togden/apiaster/images/also_in_mx_thanks_witch.jpg

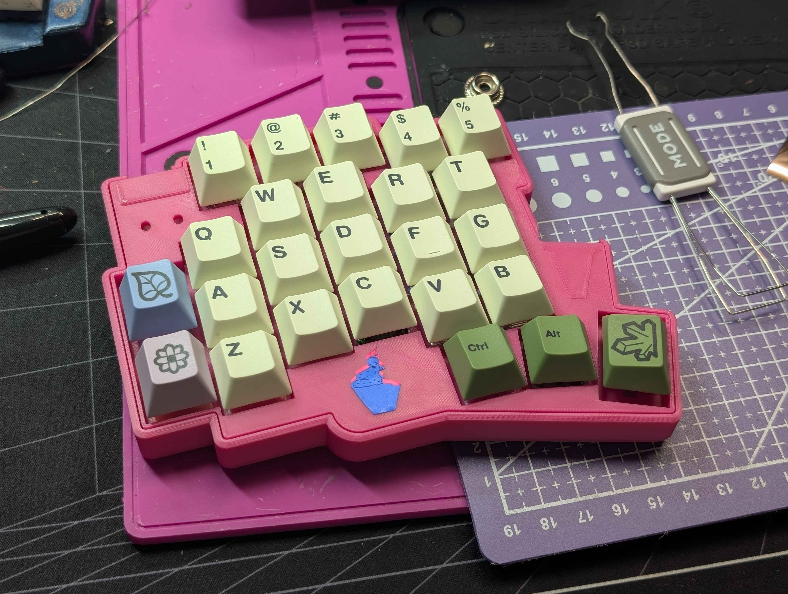
images/also_in_mx_thanks_witch.jpg
