togden/apiaster/images/ambient_choc.png

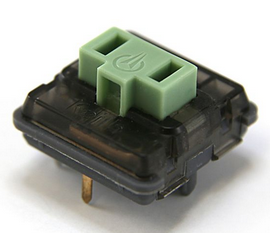
images/ambient_choc.png
