togden/apiaster/images/baby_kangaroo_mx.png

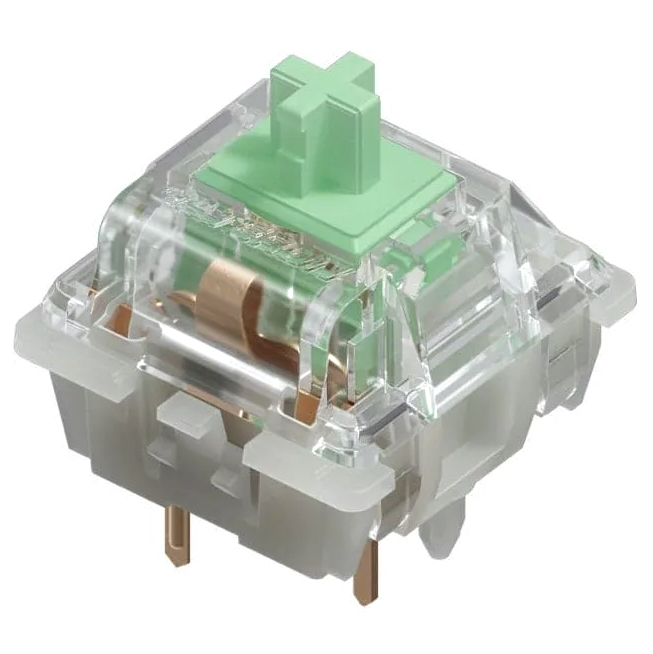
images/baby_kangaroo_mx.png
