togden/apiaster/images/coin_cell.png

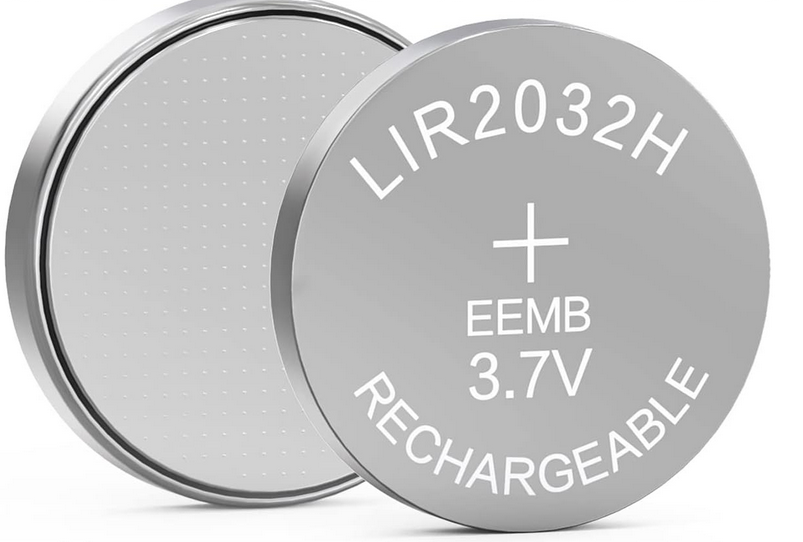
images/coin_cell.png
