togden/apiaster/images/front_angle.jpg

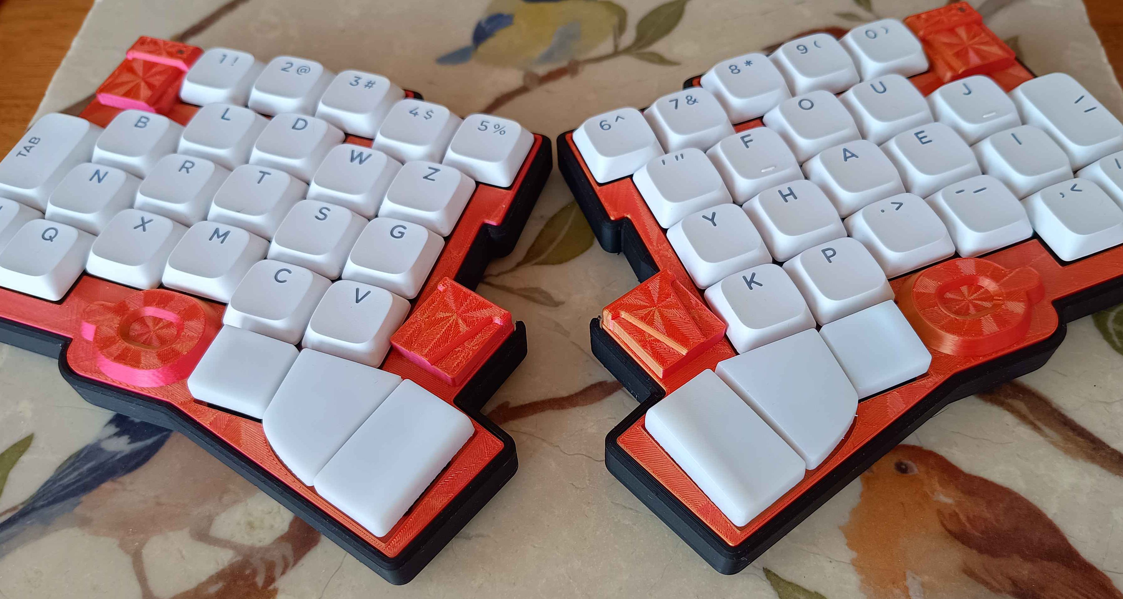
images/front_angle.jpg
