togden/apiaster/images/lipo-battery.png

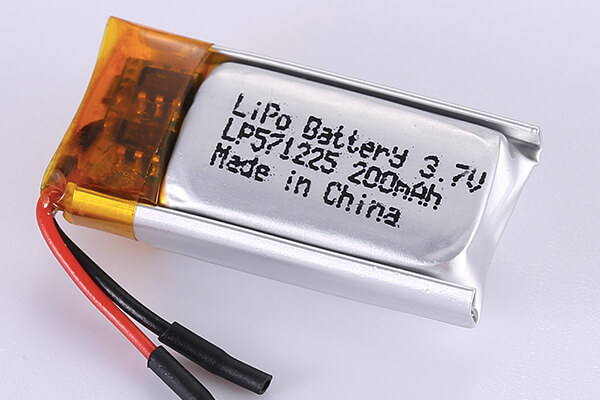
images/lipo-battery.png
