togden/apiaster/images/pom_chocv2.png

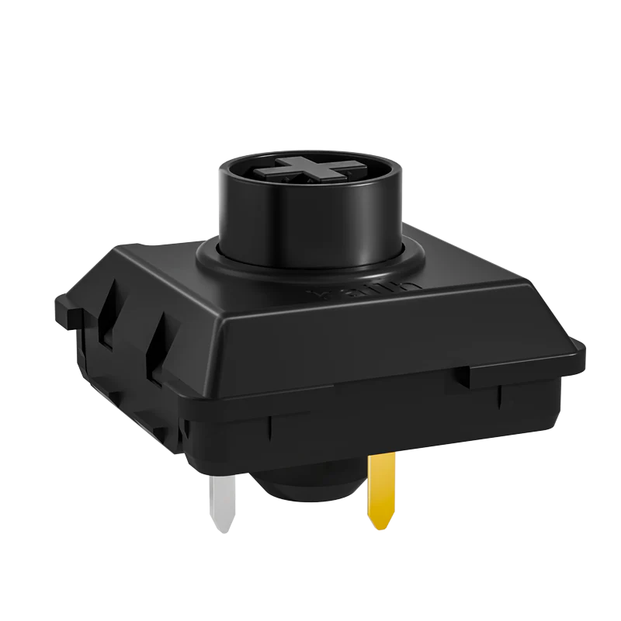
images/pom_chocv2.png
