togden/apiaster/images/rp2040-zero.png

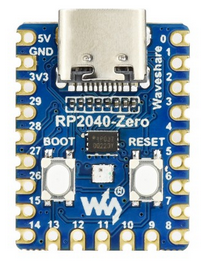
images/rp2040-zero.png
