togden/apiaster/images/show_rpi_caps.jpg

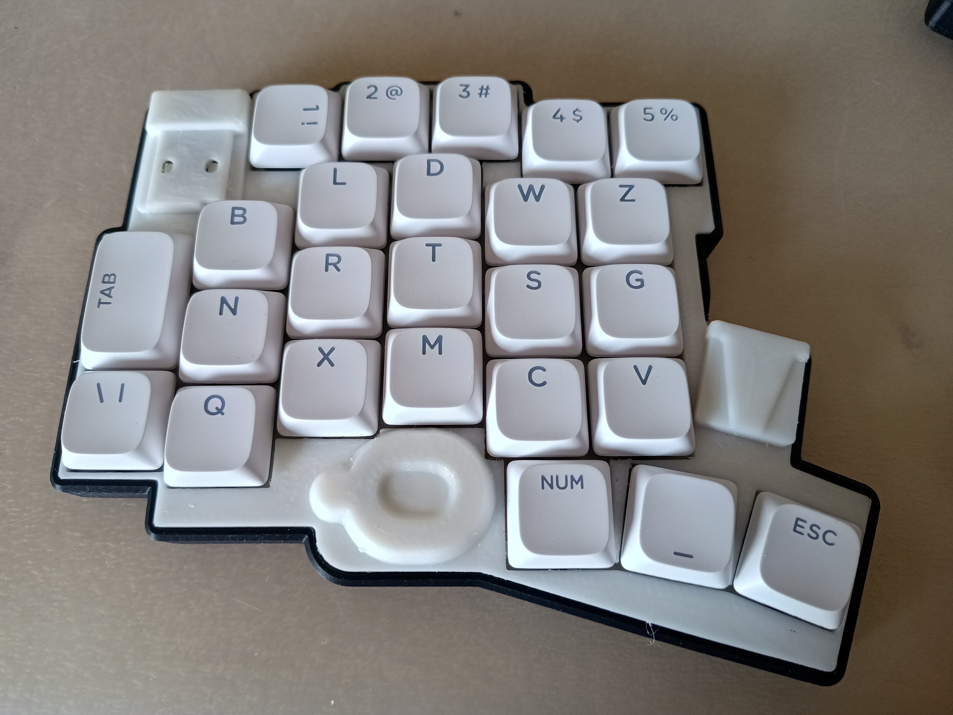
images/show_rpi_caps.jpg
