togden/apiaster/images/show_rpi_no_caps.jpg

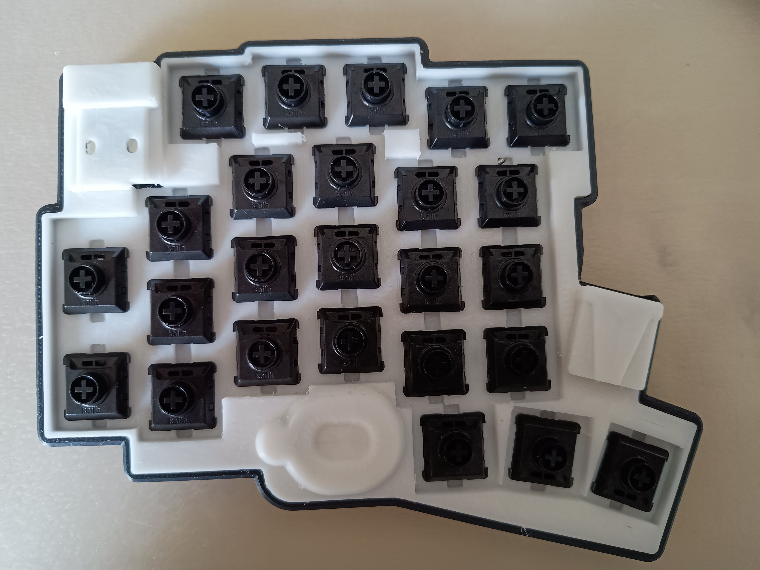
images/show_rpi_no_caps.jpg
