togden/apiaster/images/thickness.jpg

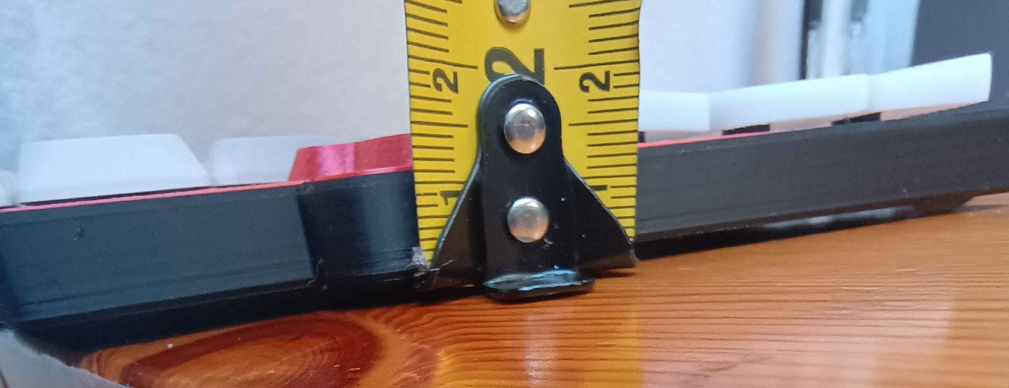
images/thickness.jpg
