togden/apiaster/images/upper.jpg

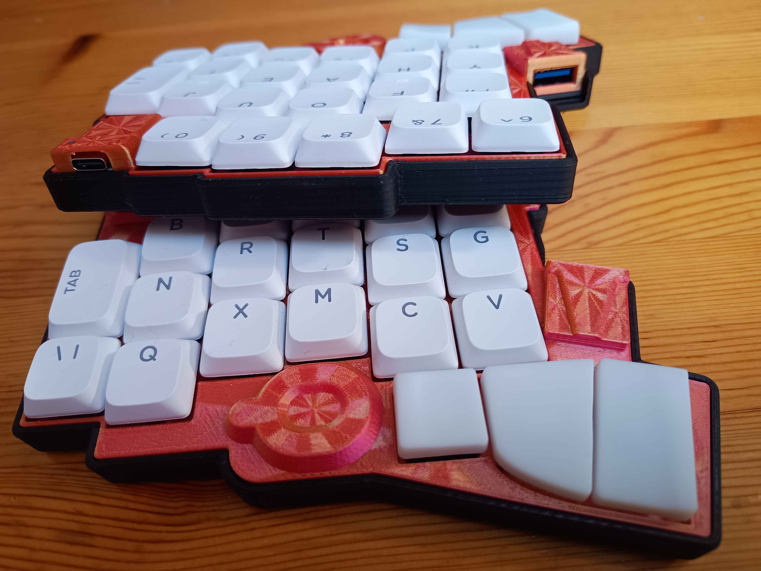
images/upper.jpg
