togden/apiaster/images/xiao.png

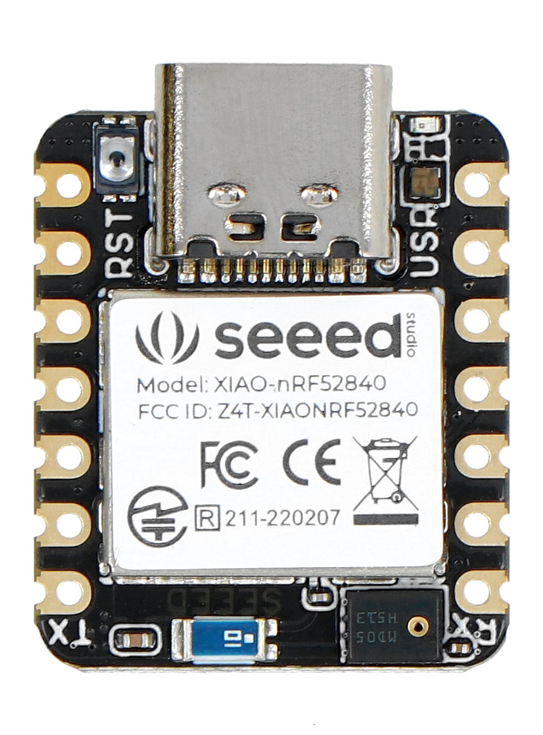
images/xiao.png
