togden/apiaster/images/build-guide/1_base_pcb_3_diodes.jpg

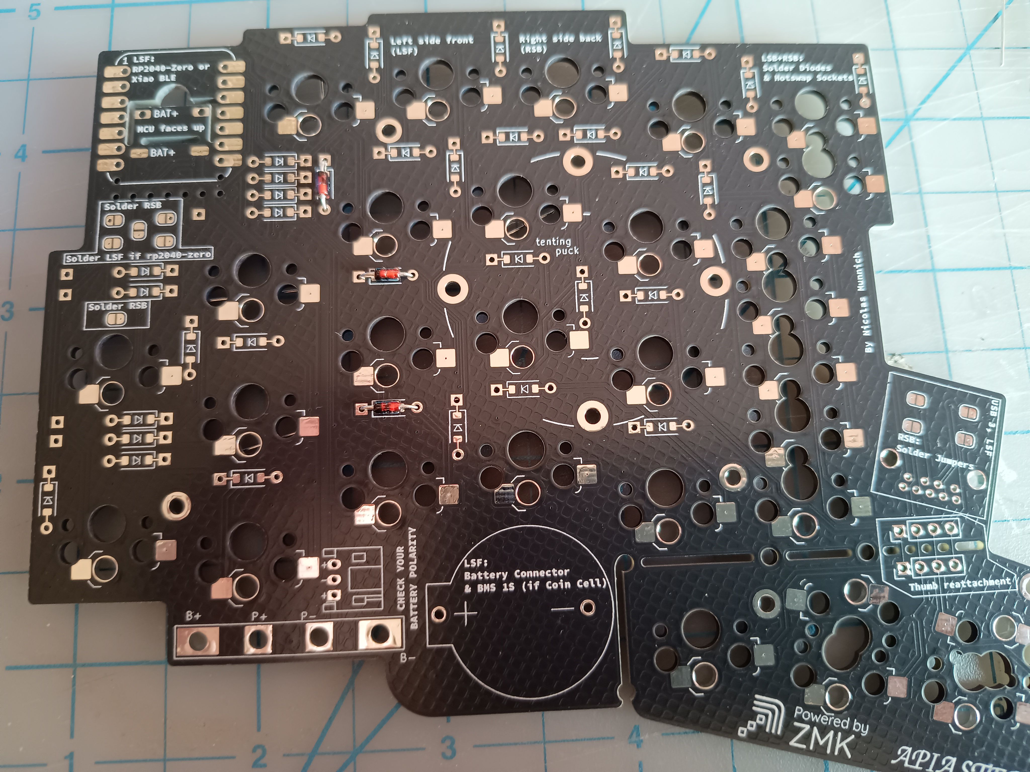
images/build-guide/1_base_pcb_3_diodes.jpg
