togden/apiaster/images/build-guide/5_check_orientation.jpg

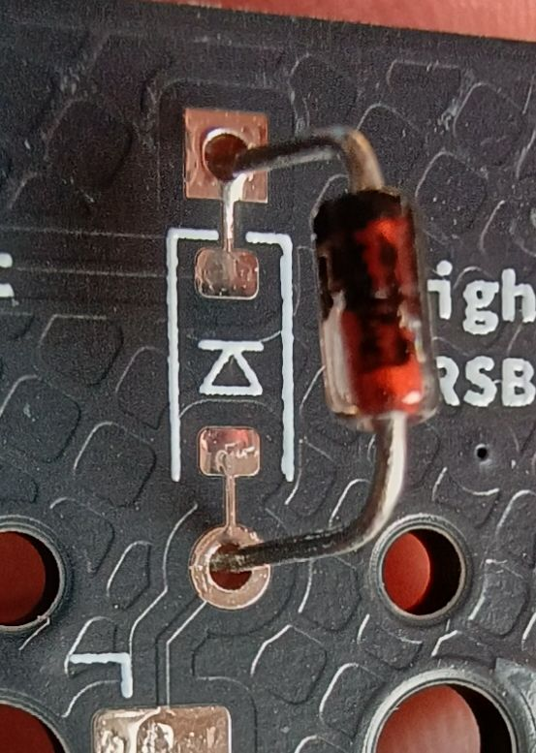
images/build-guide/5_check_orientation.jpg
