togden/apiaster/images/ordering-guide/xvx-caps.png

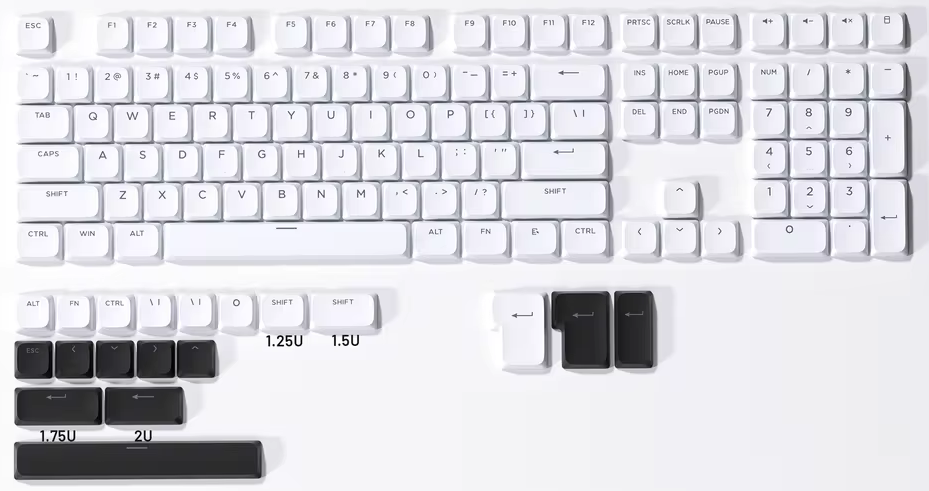
images/ordering-guide/xvx-caps.png
