togden/apiaster/pcb/apiaster-choc/apiaster.kicad_sch

## KiCad design pcb/apiaster-choc/apiaster.kicad_sch (2025-03-03)

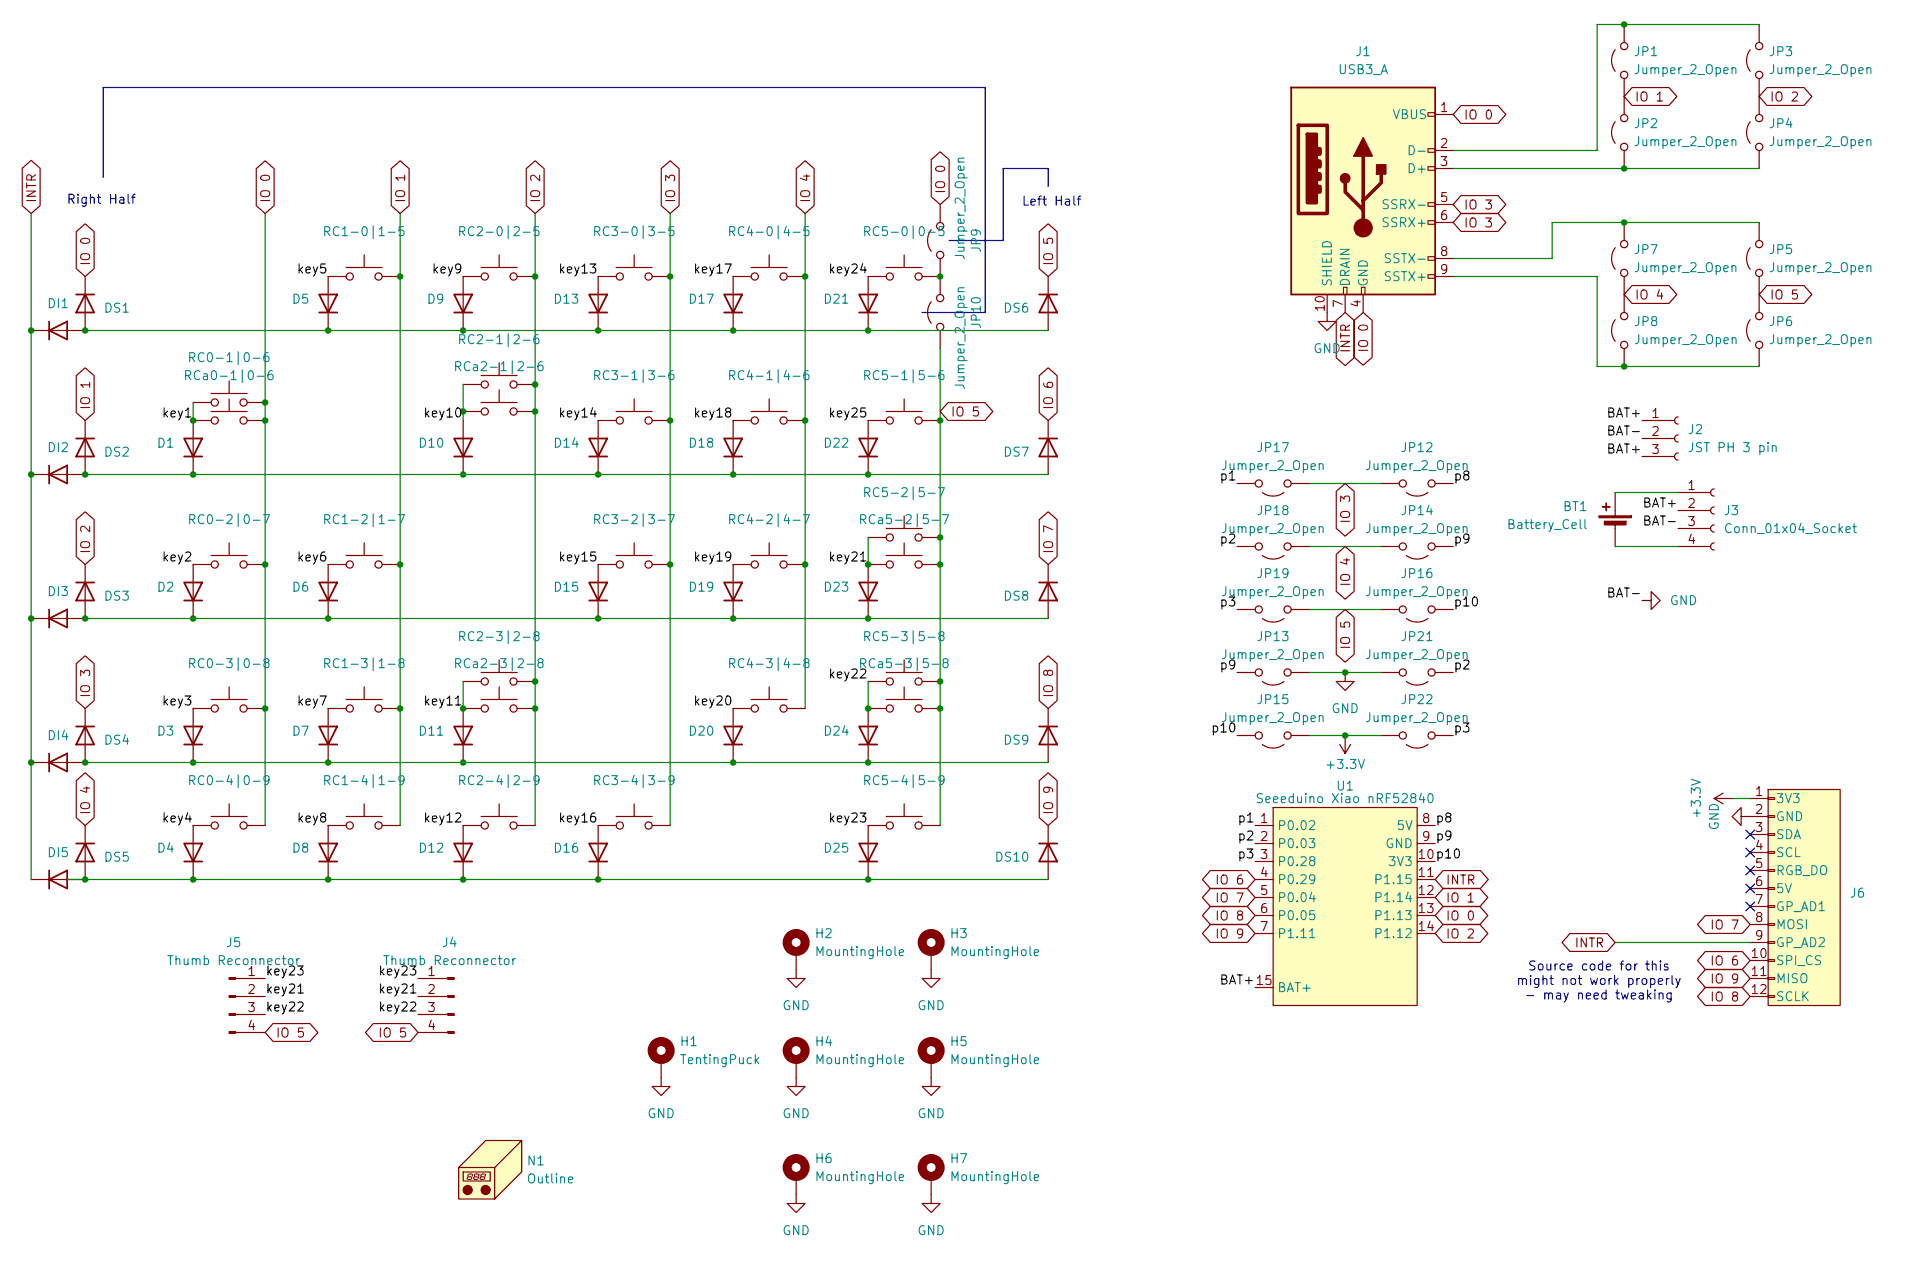
[picture p76: schematic apiaster.kicad_sch]

Parts:
BT1: Battery_Cell; BatteryHolder_CR2032_20mm
D1, D2, D3, D4, D5, D6, D7, D8, D9, D10, D11, D12, D13, D14, D15, D16, D17, D18, D19, D20, D21, D22, D23, D24, D25: 1N4148; D-SOD123-DO35-7mm-horizontal-combo_rev
DI1, DI2, DI3, DI4, DI5: 1N4148; D-SOD123-DO35-7mm-horizontal-combo_rev
DS1, DS2, DS3, DS4, DS5, DS6, DS7, DS8, DS9, DS10: 1N4148; D-SOD123-DO35-7mm-horizontal-combo
H1: TentingPuck
H2, H3, H4, H5, H6, H7: MountingHole; MountingHole_2.2mm_M2_DIN965_Pad
J1: USB3_A; USB3_A_Aliexpress
J2: JST PH 3 pin; JST_PH_S3B-PH-K_1x03_P2.00mm_Horizontal
J3: Conn_01x04_Socket; BMS 1S
J4, J5: Thumb Reconnector; PinHeader_1x04_P2.54mm_Vertical
J6: vik-keyboard-connector-vertical
JP1, JP2, JP3, JP4, JP5, JP6, JP7, JP8, JP9, JP10, JP12, JP13, JP14, JP15, JP16, JP17, JP18, JP19, JP21, JP22: Jumper_2_Open; SolderJumper-2_P1.3mm_Open_RoundedPad1.0x1.5mm
N1: Outline
RC0-1|0-6, RC2-1|2-6, RC2-3|2-8: SW_Push; Chocv12_reversible_hotswap_no_middle
RC0-2|0-7, RC0-3|0-8, RC0-4|0-9, RC1-0|1-5, RC1-2|1-7, RC1-3|1-8, RC1-4|1-9, RC2-0|2-5, RC2-4|2-9, RC3-0|3-5, RC3-1|3-6, RC3-2|3-7, RC3-4|3-9, RC4-0|4-5, RC4-1|4-6, RC4-2|4-7, RC4-3|4-8, RC5-0|0-5, RC5-1|5-6, RC5-2|5-7, RC5-3|5-8, RC5-4|5-9: SW_Push; Chocv12_reversible_hotswap
RCa0-1|0-6, RCa5-2|5-7, RCa5-3|5-8: SW_Push; Chocv12_reversible_hotswap
RCa2-1|2-6, RCa2-3|2-8: SW_Push; Chocv12_reversible_hotswap_no_middle
U1: Seeeduino Xiao nRF52840; xiao+zero_combo

Connections:
+3.3V: J6.1 (3V3), JP15.2 (B), JP22.1 (A)
BAT+: J2.1, J2.3, J3.2, U1.15 (BAT+)
GND: H1.1, H2.1, H3.1, H4.1, H5.1, H6.1, H7.1, J1.10 (SHIELD), J2.2, J3.3, J6.2 (GND), JP13.2 (B), JP21.1 (A)
INTR: DI1.1 (K), DI2.1 (K), DI3.1 (K), DI4.1 (K), DI5.1 (K), J1.7 (DRAIN), J6.9 (GP_AD2), U1.11 (P1.15)
IO 0: DS1.1 (K), J1.1 (VBUS), J1.4 (GND), JP9.1 (A), RC0-1|0-6.1, RC0-2|0-7.1, RC0-3|0-8.1, RC0-4|0-9.1, RCa0-1|0-6.1, U1.13 (P1.13)
IO 1: DS2.1 (K), JP1.1 (A), JP2.2 (B), RC1-0|1-5.1, RC1-2|1-7.1, RC1-3|1-8.1, RC1-4|1-9.1, U1.12 (P1.14)
IO 2: DS3.1 (K), JP3.1 (A), JP4.2 (B), RC2-0|2-5.1, RC2-1|2-6.1, RC2-3|2-8.1, RC2-4|2-9.1, RCa2-1|2-6.1, RCa2-3|2-8.1, U1.14 (P1.12)
IO 3: DS4.1 (K), J1.5 (SSRX-), J1.6 (SSRX+), JP12.1 (A), JP17.2 (B), RC3-0|3-5.1, RC3-1|3-6.1, RC3-2|3-7.1, RC3-4|3-9.1
IO 4: DS5.1 (K), JP7.1 (A), JP8.2 (B), JP14.1 (A), JP18.2 (B), RC4-0|4-5.1, RC4-1|4-6.1, RC4-2|4-7.1, RC4-3|4-8.1
IO 5: DS6.1 (K), J4.4, J5.4, JP5.1 (A), JP6.2 (B), JP10.2 (B), JP16.1 (A), JP19.2 (B), RC5-1|5-6.1, RC5-2|5-7.1, RC5-3|5-8.1, RC5-4|5-9.1, RCa5-2|5-7.1, RCa5-3|5-8.1
IO 6: DS7.1 (K), J6.10 (SPI_CS), U1.4 (P0.29)
IO 7: DS8.1 (K), J6.8 (MOSI), U1.5 (P0.04)
IO 8: DS9.1 (K), J6.12 (SCLK), U1.6 (P0.05)
IO 9: DS10.1 (K), J6.11 (MISO), U1.7 (P1.11)
unnamed: BT1.1 (+), J3.1
unnamed: BT1.2 (-), J3.4
unnamed: D1.1 (K), D10.1 (K), D14.1 (K), D18.1 (K), D22.1 (K), DI2.2 (A), DS2.2 (A), DS7.2 (A)
unnamed: D3.1 (K), D7.1 (K), D11.1 (K), D20.1 (K), D24.1 (K), DI4.2 (A), DS4.2 (A), DS9.2 (A)
unnamed: D4.1 (K), D8.1 (K), D12.1 (K), D16.1 (K), D25.1 (K), DI5.2 (A), DS5.2 (A), DS10.2 (A)
unnamed: D5.1 (K), D9.1 (K), D13.1 (K), D17.1 (K), D21.1 (K), DI1.2 (A), DS1.2 (A), DS6.2 (A)
unnamed: D2.1 (K), D6.1 (K), D15.1 (K), D19.1 (K), D23.1 (K), DI3.2 (A), DS3.2 (A), DS8.2 (A)
unnamed: J1.2 (D-), JP1.2 (B), JP3.2 (B)
unnamed: J1.3 (D+), JP2.1 (A), JP4.1 (A)
unnamed: J1.8 (SSTX-), JP5.2 (B), JP7.2 (B)
unnamed: J1.9 (SSTX+), JP6.1 (A), JP8.1 (A)
unnamed: JP9.2 (B), JP10.1 (A), RC5-0|0-5.1
key1: D1.2 (A), RC0-1|0-6.2, RCa0-1|0-6.2
key2: D2.2 (A), RC0-2|0-7.2
key3: D3.2 (A), RC0-3|0-8.2
key4: D4.2 (A), RC0-4|0-9.2
key5: D5.2 (A), RC1-0|1-5.2
key6: D6.2 (A), RC1-2|1-7.2
key7: D7.2 (A), RC1-3|1-8.2
key8: D8.2 (A), RC1-4|1-9.2
key9: D9.2 (A), RC2-0|2-5.2
key10: D10.2 (A), RC2-1|2-6.2, RCa2-1|2-6.2
key11: D11.2 (A), RC2-3|2-8.2, RCa2-3|2-8.2
key12: D12.2 (A), RC2-4|2-9.2
key13: D13.2 (A), RC3-0|3-5.2
key14: D14.2 (A), RC3-1|3-6.2
key15: D15.2 (A), RC3-2|3-7.2
key16: D16.2 (A), RC3-4|3-9.2
key17: D17.2 (A), RC4-0|4-5.2
key18: D18.2 (A), RC4-1|4-6.2
key19: D19.2 (A), RC4-2|4-7.2
key20: D20.2 (A), RC4-3|4-8.2
key21: D23.2 (A), J4.2, J5.2, RC5-2|5-7.2, RCa5-2|5-7.2
key22: D24.2 (A), J4.3, J5.3, RC5-3|5-8.2, RCa5-3|5-8.2
key23: D25.2 (A), J4.1, J5.1, RC5-4|5-9.2
key24: D21.2 (A), RC5-0|0-5.2
key25: D22.2 (A), RC5-1|5-6.2
p1: JP17.1 (A), U1.1 (P0.02)
p2: JP18.1 (A), JP21.2 (B), U1.2 (P0.03)
p3: JP19.1 (A), JP22.2 (B), U1.3 (P0.28)
p8: JP12.2 (B), U1.8 (5V)
p9: JP13.1 (A), JP14.2 (B), U1.9 (GND)
p10: JP15.1 (A), JP16.2 (B), U1.10 (3V3)

Notes on the sheet:
Source code for this might not work properly - may need tweaking
Right Half
Left Half
